SafiSoftProgramming/Self_Balance_Robot_Project_SafiSoft/SafiSoft Self Balance Robot Project/RoboBoy Android App Screenshots Download for free/Frame 22.png

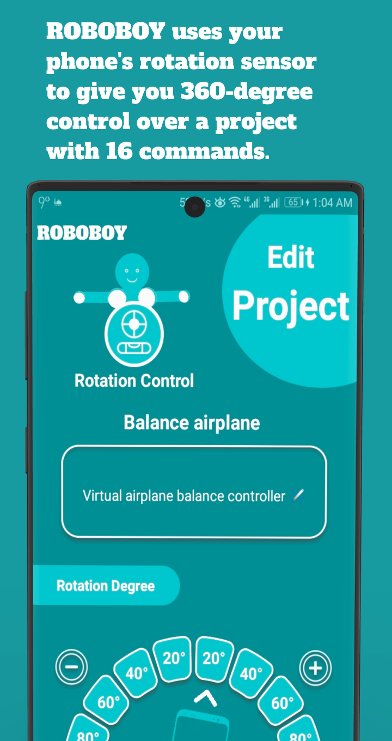
SafiSoft Self Balance Robot Project/RoboBoy Android App Screenshots Download for free/Frame 22.png
