SafiSoftProgramming/Self_Balance_Robot_Project_SafiSoft/SafiSoft Self Balance Robot Project/Self Balance Robot Files/Self_Balance_Robot_Dimensions.png

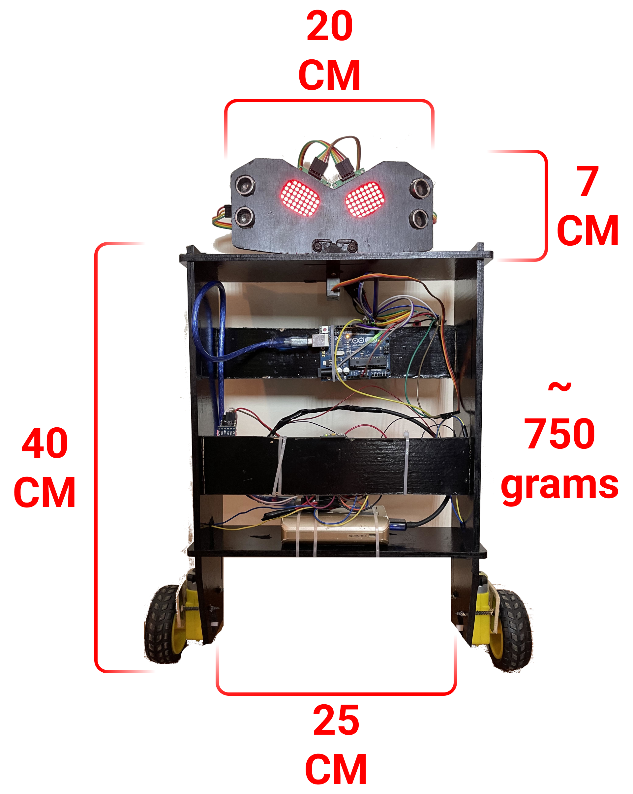
SafiSoft Self Balance Robot Project/Self Balance Robot Files/Self_Balance_Robot_Dimensions.png
