SafiSoftProgramming/Self_Balance_Robot_Project_SafiSoft/SafiSoft Self Balance Robot Project/Robot Head Files/Components/WhatsApp Image 2022-01-02 at 9.13.22 PM.jpeg

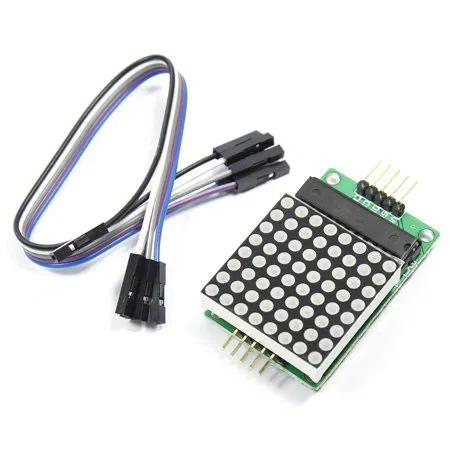
SafiSoft Self Balance Robot Project/Robot Head Files/Components/WhatsApp Image 2022-01-02 at 9.13.22 PM.jpeg
