SafiSoftProgramming/Self_Balance_Robot_Project_SafiSoft/SafiSoft Self Balance Robot Project/Self Balance Robot Files/Components/WhatsApp Image 2022-01-02 at 9.13.24 PM (1).jpeg

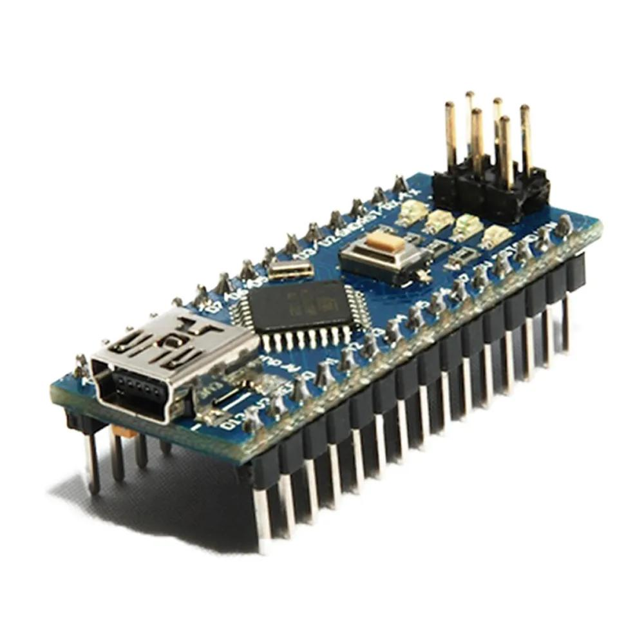
SafiSoft Self Balance Robot Project/Self Balance Robot Files/Components/WhatsApp Image 2022-01-02 at 9.13.24 PM (1).jpeg
