SafiSoftProgramming/Self_Balance_Robot_Project_SafiSoft/SafiSoft Self Balance Robot Project/Robot Head Files/Robot_Head_Design_Print_as_A4.png

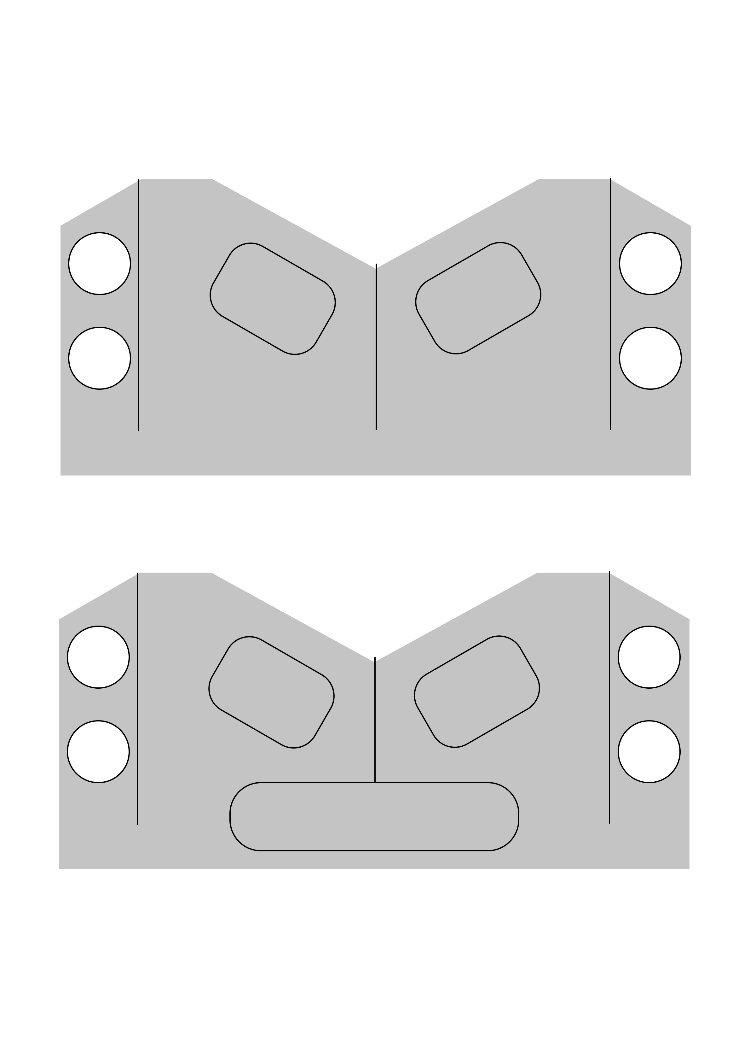
SafiSoft Self Balance Robot Project/Robot Head Files/Robot_Head_Design_Print_as_A4.png
